ErikMiyoshi/WeatherStation/FW/WeatherStation/components/app_button/include/app_button.h

void app_button_init(void);

int adc_get_single(void);
int battery_get_voltage(void);
bool is_button_left_pressed(void);
bool is_button_center_pressed(void);
bool is_button_right_pressed(void);

bool is_joystick_pressed_right(void);
bool is_joystick_pressed_left(void);
